yuburoll/phalwol/images/phalwolPhotoHeader.jpg

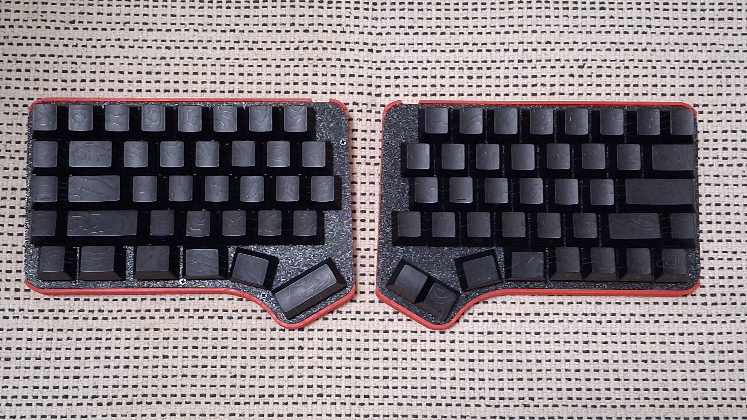
images/phalwolPhotoHeader.jpg
