yuburoll/phalwol/case/step/phalwolCaseBuffedL.stp

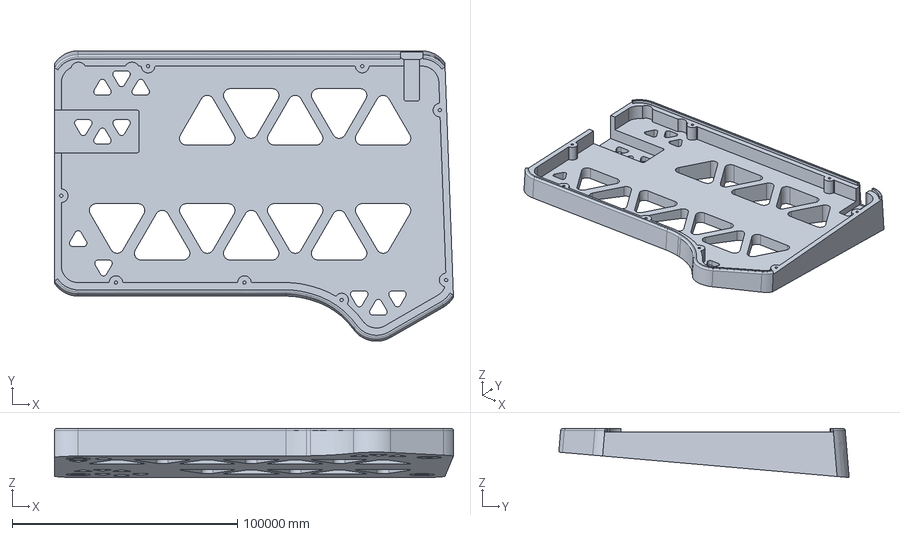
[picture p20: CAD file, 2026-06-18]
case/step/phalwolCaseBuffedL.stp
176978.3 x 128826.0 x 21788.3 mm
