yuburoll/phalwol/case/step/phalwolCaseR.stp

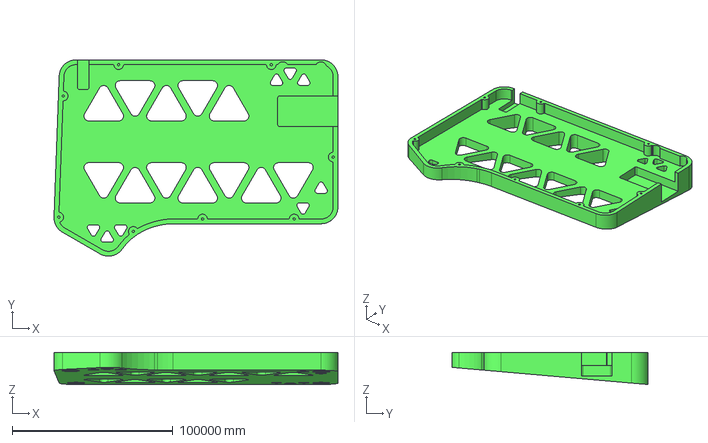
[picture p21: CAD file, 2026-06-18]
case/step/phalwolCaseR.stp
176693.6 x 122140.4 x 19954.9 mm
